co2monnz/CO2Monitor/pcb/CO2 Monitor V0.5 SMD/CO2Monitor-SMD-V0.5.render.png

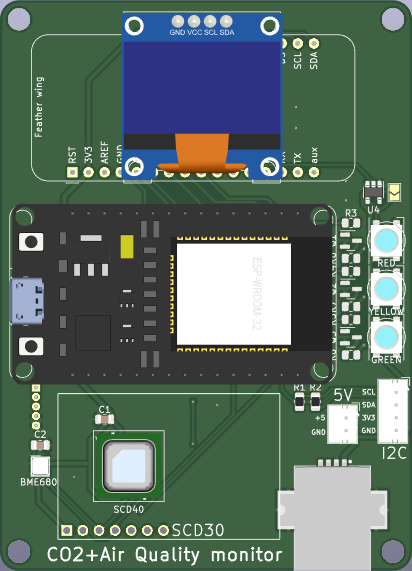
pcb/CO2 Monitor V0.5 SMD/CO2Monitor-SMD-V0.5.render.png
