co2monnz/CO2Monitor/pcb/CO2 Monitor V0.5 through-hole/14-scd30.jpg

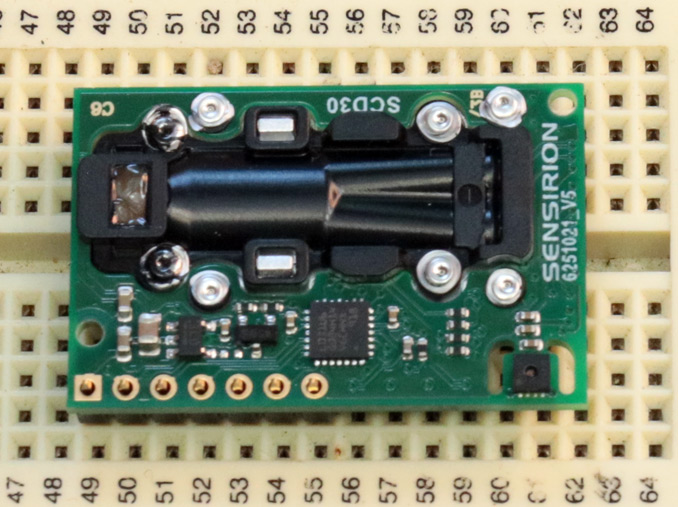
pcb/CO2 Monitor V0.5 through-hole/14-scd30.jpg
