co2monnz/CO2Monitor/include/bme680.h

#ifndef _BME680_H
#define _BME680_H

#include <Arduino.h>
#include "globals.h"
#include <config.h>
#include <messageSupport.h>
#include <Wire.h>
#include <model.h>
#include <EEPROM.h>
#include "bsec.h"

class BME680 {
public:
  BME680(TwoWire* pwire, Model* _model, updateMessageCallback_t _updateMessageCallback);
  ~BME680();

  boolean readBme680();
  uint32_t getInterval();

private:
  Bsec* bme680;
  Model* model;
  updateMessageCallback_t updateMessageCallback;

  static void bme680Loop(void* pvParameters);

  void checkIaqSensorStatus();
  void loadState(void);
  void updateState(void);

};

#endif
