co2monnz/CO2Monitor/include/i2c.h

#ifndef _I2C_H
#define _I2C_H

#include "globals.h"

#define I2C_MUTEX_DEF_WAIT pdMS_TO_TICKS(5000)

namespace I2C {
#define SSD1306_I2C_ADR 0x3C
#define SCD30_I2C_ADR 0x61
#define SCD40_I2C_ADR 0x62
#define SPS30_I2C_ADR 0x69
#define BME680_I2C_ADR 0x76

  void initI2C();

  boolean takeMutex(TickType_t blockTime);
  void giveMutex();

  boolean lcdPresent();
  boolean scd30Present();
  boolean scd40Present();
  boolean sps30Present();
  boolean bme680Present();
}
#endif
